shaise/DiSE/src/Firmware/DavinciKbd/Core/Inc/version.h

/*
 * version.h
 *
 *  Created on: Sep 20, 2021
 *      Author: shai
 */

#ifndef INC_VERSION_H_
#define INC_VERSION_H_

/* v1.00 : initial version
 *
 */
#define VER_MAJOR   1
#define VER_MINOR	0



#endif /* INC_VERSION_H_ */
